jankae/LCR/DDSFilter.asc

A1: sample; vt=0.5; vhigh=1e6 vlow=-1e6
B1: bv; V=int(V(vs0)*1638)/1638
C1: cap; 10p
C2: cap; 100n
C3: cap; 2n2
C4: cap; 4n7
C5: cap; 100n
C6: cap; 100n
C7: cap; 100n
C8: cap; 0
C11: cap; 10µ IC=-1.25
C12: cap; 100p
L1: ind; 100µ
R1: res; 100
R2: res; 100k
R3: res; 1000k
R4: res; 300
R5: res; 470
R6: res; 1000k
R7: res; 2k
R8: res; 1k
R9: res; 100
R10: res; 3k3
R11: res; 2k
R12: res; 10k
R13: res; 10k
R14: res; 1000k
R15: res; 1000k
R16: res; 2k
R17: res; 2k
R18: res; 10k
R19: res; 10k
R20: res; 100
U1: TL072
U2: TL072
U3: TL072
U4: TL072
U5: TL072
U6: TL072
U7: TL072
U8: TL072
U9: TL072
U10: TL072
U11: TL072
V1: voltage; 12
V2: voltage; -12
V3: voltage; ""; AC 1
V4: voltage; 0
V5: voltage; SINE(1.25 1.25 {f0})
V6: voltage; PULSE(0 1 0 1n 1n 100n {1/fs})
Named nets: 0, -12, +12, sq, s0, fs, vs0
.tran .1m uic
;tran 0 3m 0 1u
.options plotwinsize=0
.param f0=100k fs=1000k
.lib opamp.sub
;ac dec 20 20 2000k
