jankae/LCR/Draft1.asc

C1: cap; 38p3
C2: cap; 144p
C3: cap; 175p
C4: cap; 144p
C5: cap; 7p15
C6: cap; 7p15
C7: cap; 38p3
L1: ind; 0µ38
L2: ind; 0µ38
L3: ind; 0µ38
R1: res; 50
R2: res; 50
R3: res; 50
R4: res; 50
V1: voltage; ""; AC 1
Named nets: 0
.ac dec 20000 6750k 30750k
