jankae/LCR/Draft2.asc

L1: ind2; 200n
L2: ind2; 400n
L3: ind2; 200n
L4: ind2; 400n
R1: res; 50
R2: res; 50
R3: res
R6: res; 50
V1: voltage; ""; AC 1
Named nets: 0
K1 L1 L2 1
.ac dec 100 2000k 3200000k
K2 L3 L4 1
