jankae/LCR/Draft3.asc

C1: cap; 10n
C2: cap; 9n
C3: cap; 10.7n
C4: cap; 3n8
C5: cap; 26n
R1: res; 16k
R2: res; 16k
R3: res; 16k
R4: res; 16k
R5: res; 16k
U1: opamp
U2: opamp
V1: voltage; SINE(0 1 700); AC 1
Named nets: 0
;ac dec 20 10 10k
.lib opamp.sub
.tran 5m
