jankae/LCR/software/LCRMeter/Application/GUI/Unit.hpp

#ifndef COMMON_H_
#define COMMON_H_

#include <stdint.h>
#include <stddef.h>
#include <stdlib.h>
#include <string.h>
#include "util.h"

#define COORDS(v1, v2)	((coords_t){(int16_t) (v1), (int16_t) (v2)})
#define SIZE(v1, v2)	COORDS(v1, v2)

const coords_t operator+(coords_t const& lhs, coords_t const& rhs);
const coords_t operator-(coords_t const& lhs, coords_t const& rhs);

namespace Unit {

using unit = struct unit {
	/* name length up to 3 (plus string terminator) */
	char name[4];
	uint32_t factor;
};

//typedef const unitElement_t *Unit::unit[];

extern const unit *Current[], *Voltage[], *Power[], *Temperature[],
		*Resistance[], *Energy[], *Time[], *Memory[], *Capacity[], *Percent[],
		*Charge[], *Weight[], *Force[], *None[], *Hex[], *Frequency[], *Distance[];
extern const int32_t null, maxPercent;

uint32_t LeastDigitValueFromString(const char *s,
		const unit *unit[]);

void StringFromValue(char *to, uint8_t len, int32_t val,
		const unit *unit[]);

using SIPrefix = struct {
	char name;
	float factor;
};
static constexpr SIPrefix SI_prefixes[] = {
		{'f', 1E-15f},
		{'p', 1E-12f},
		{'n', 1E-9f},
		{'u', 1E-6f},
		{'m', 1E-3f},
		{' ', 1E-0f},
		{'k', 1E+3f},
		{'M', 1E+6f},
		{'G', 1E+9f},
		{'T', 1E+12f},
		{'P', 1E+15f},
};

bool SIStringFromFloat(char* to, uint8_t len, float val, char smallest_prefix = 'f');

uint8_t ValueFromString(int32_t *value, char *s, const unit *unit[]);
int32_t ValueFromString(const char *s, uint32_t multiplier);

}

#endif
