jankae/LCR/software/LCRMeter/Application/GUI/MenuBool.hpp

/*
 * MenuBool.hpp
 *
 *  Created on: Jun 9, 2019
 *      Author: jan
 */

#ifndef MENUBOOL_HPP_
#define MENUBOOL_HPP_

#include "menuentry.hpp"

class MenuBool : public MenuEntry {
public:
	MenuBool(const char *name, bool *value, void (*cb)(void*, Widget*) = nullptr,
			void *ptr = nullptr, const char *off_string = "OFF", const char *on_string = "ON");

private:
	void draw(coords_t offset) override;
	void input(GUIEvent_t *ev) override;

	Widget::Type getType() override { return Widget::Type::MenuBool; };

	static constexpr color_t Background = COLOR_BG_DEFAULT;
	static constexpr color_t Foreground = COLOR_FG_DEFAULT;
	static constexpr color_t ColorOn = COLOR(0, 192, 0);
	static constexpr color_t ColorOff = COLOR(238, 0, 0);
	static constexpr uint8_t MaxNameLength = 25;
	static constexpr uint8_t MaxStringLength = 5;
	static constexpr const font_t *fontName = &Font_Medium;
	static constexpr const font_t *fontValue = &Font_Big;

    void (*callback)(void *ptr, Widget* source);
    void *cb_ptr;
    bool *value;
    char name[MaxNameLength + 1];
    char on[MaxStringLength + 1];
    char off[MaxStringLength + 1];
};



#endif /* MENUBOOL_HPP_ */
