jankae/LCR/software/LCRMeter/Application/GUI/graph.hpp

#ifndef GRAPH_H_
#define GRAPH_H_

#include "widget.hpp"
#include "display.h"

#include "Unit.hpp"

class Graph : public Widget {
public:
	Graph(const int32_t *values, uint16_t num, uint16_t height, color_t color, const Unit::unit *unit[]);

	void newColor(color_t color);
	void newData(const int32_t *data);
private:
	void draw(coords_t offset) override;

	Widget::Type getType() override { return Widget::Type::Graph; };

	static constexpr color_t Background = COLOR_BG_DEFAULT;
	static constexpr color_t Border = COLOR_FG_DEFAULT;

    const int32_t *values;
    color_t color;
    const Unit::unit **unit;
};

#endif
